Cheet0sDelet0s/cheetoPet/sprites/outside mockup.png

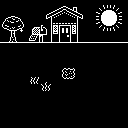
sprites/outside mockup.png
