Cheet0sDelet0s/cheetoPet/cheetoPet-V2/DisplayTest.cpp

#include "drivers/Platform.h"
#include "ui/Ui.h"
#include "ui/Menu.h"

#include "drivers/display/fonts/Font5x7.h"

#include <algorithm>
#include <iostream>

using namespace display;

ui::Menu mainMenu(
    20,     // x
    30,     // y
    200,    // width
    240,    // height
    32,     // item height
    5       // spacing
);

ui::Menu settingsMenu(
    20,     // x
    30,     // y
    200,    // width
    240,    // height
    32,     // item height
    5       // spacing
);

void openSettings(ui::Ui& ui)
{
    ui.push(&settingsMenu);
}

void openMainMenu(ui::Ui& ui)
{
    ui.push(&mainMenu);
}

const ui::Theme themey = {
    .background = display::Color(0x0000),
    .primary = display::Color(0xfb40),
    .focused = display::Color(0x05FF),
    .text = display::Color(0xFFFF),
    .disabled = display::Color(0x4208),
    .border = display::Color(0x6b59),
    .focusedBorder = display::Color(0xFFFF),
    .cornerRadius = 6
};

int main()
{
    platform::RTC clock;
    platform::Battery bat;
    platform::IMU imu;
    platform::Audio audio;
    platform::Display display;
    platform::Input buttons;

    ui::Ui ui(
        display,
        buttons
    );

    if (!display.begin())
        return 1;
    
    if (!buttons.begin())
        return 1;

    if (!clock.begin())
        return 1;
    
    if (!bat.begin())
        return 1;

    if (!imu.begin())
        return 1;
    
    if (!audio.begin())
        return 1;

    audio.setVolume(0.5f);
    audio.tone(440,200);
    
    imu.setMouseControlEnabled(true);

    display.fillScreen(BLACK); 

    display.setFont(fonts::Font5x7);
    display.setTextColor(WHITE);
    display.setTextSize(1);

    for (int i = 1; i < 5; i++)
    {
        mainMenu.addItem(
            "This is the main menu",
            openSettings
        );

        mainMenu.addItem(
            "It is quite main",
            openSettings
        );
    }

    for (int i = 1; i < 5; i++)
    {
        settingsMenu.addItem(
            "This is the settings menu",
            openMainMenu
        );

        settingsMenu.addItem(
            "It is quite setty",
            openMainMenu
        );
    }

    mainMenu.setTheme(themey);

    ui.push(&mainMenu);

    display.present();

    while (display.processEvents())
    {
        buttons.update();
        imu.update();
        ui.update();

        auto gyro = imu.gyro();
        auto accel = imu.acceleration();

        display.fillScreen(BLACK);

        ui.draw();

        printf(
            "gyro: %.2f %.2f %.2f\n",
            gyro.x,
            gyro.y,
            gyro.z
        );

        printf(
            "accel: %.2f %.2f %.2f\n",
            accel.x,
            accel.y,
            accel.z
        );

        static int etchX = 0;
        static int etchY = 0;

        static int circleX = 64;
        static int circleY = 64;

        static int frequency = 200;

        if (buttons.isPressed(input::Button::Up)) etchY -= 1;
        if (buttons.isPressed(input::Button::Down)) etchY += 1;
        if (buttons.isPressed(input::Button::X)) etchX += 1;
        if (buttons.isPressed(input::Button::A)) etchX -= 1;

        if (buttons.wasPressed(input::Button::B))
        {
            frequency += 30;
            if (frequency > 2000) frequency = 200;
            audio.tone(frequency, 200);
        }

        circleX = std::clamp(int(circleX + accel.z / 2), 0, 240);
        circleY = std::clamp(int(circleY + accel.x / 2), 0, 280);
        
        display.drawPixel(etchX, etchY, RED);
        display.fillCircle(circleX, circleY, 10, GREEN);

        rtc::DateTime now;

        if (clock.read(now)) {
            display.fillRect(0, 0, 175, 16, BLACK);
            display.setTextColor(WHITE);
            display.setCursor(0, 0);
            display.print("time: ");
            display.print(now.hour);
            display.print(":");
            display.print(now.minute);
            display.print(":");
            display.print(now.second);
        }

        bat.read();

        display.print("  |  battery: ");
        display.print(bat.getPercentage() / 100);
        display.print("%");

        display.present();
    }

    return 0;
}
